JDet-74/VIDEO2SCART/3DPrint/case01.jpg

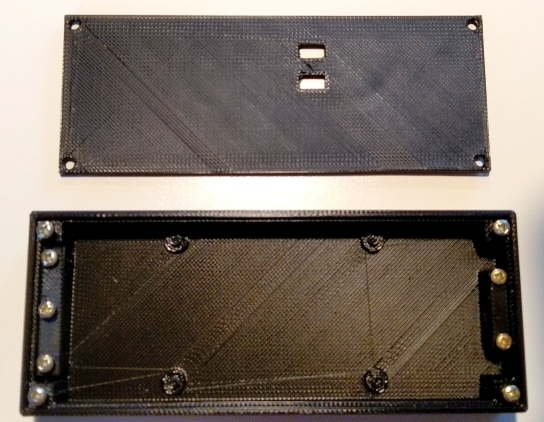
3DPrint/case01.jpg
