JDet-74/VIDEO2SCART/3DPrint/case02.jpg

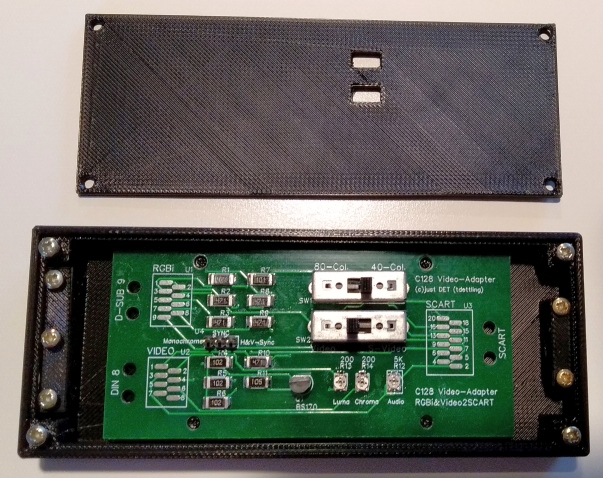
3DPrint/case02.jpg
