JDet-74/VIDEO2SCART/3DPrint/case03.jpg

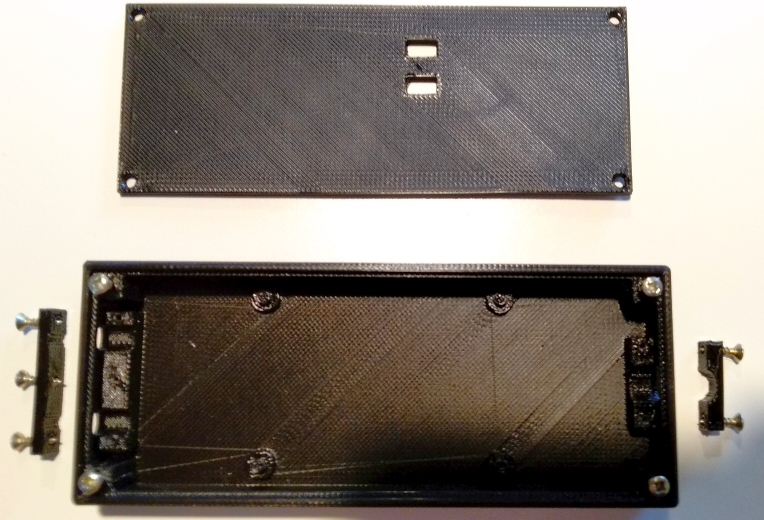
3DPrint/case03.jpg
