JDet-74/VIDEO2SCART/3DPrint/case04.jpg

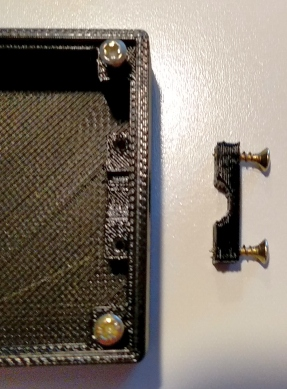
3DPrint/case04.jpg
