JDet-74/VIDEO2SCART/3DPrint/case05.jpg

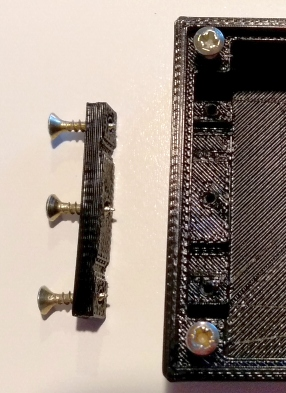
3DPrint/case05.jpg
