JDet-74/VIDEO2SCART/3DPrint/case06.jpg

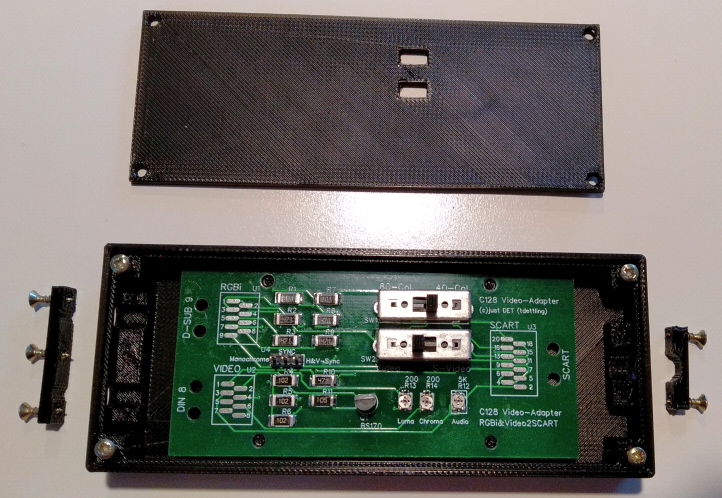
3DPrint/case06.jpg
