JDet-74/VIDEO2SCART/cable_howto/cable_03.jpg

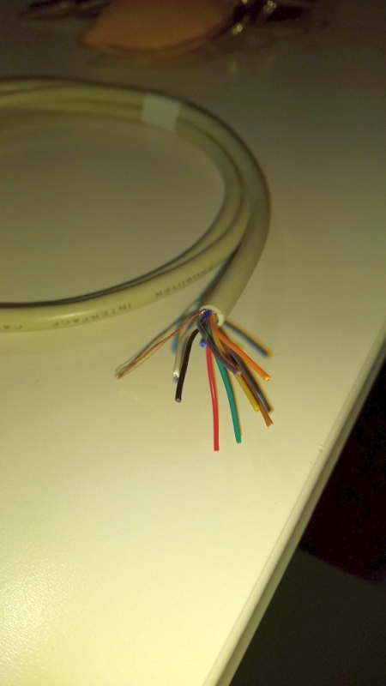
cable_howto/cable_03.jpg
