JDet-74/VIDEO2SCART/cable_howto/cable_04.jpg

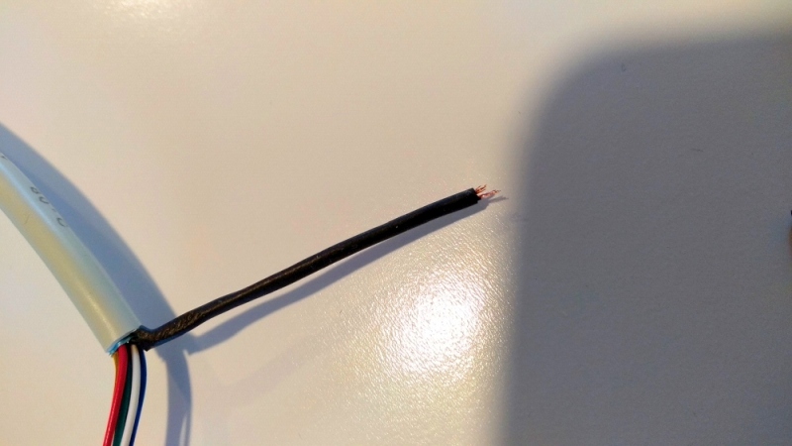
cable_howto/cable_04.jpg
