JDet-74/VIDEO2SCART/cable_howto/cable_04b.jpg

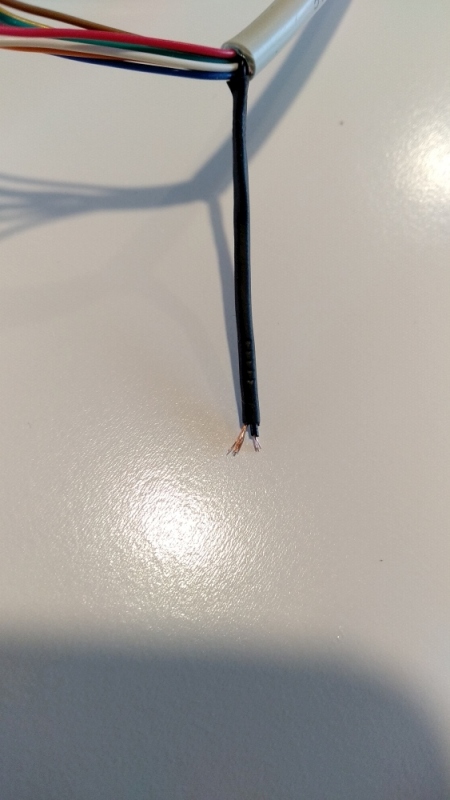
cable_howto/cable_04b.jpg
