JDet-74/VIDEO2SCART/cable_howto/cable_05.jpg

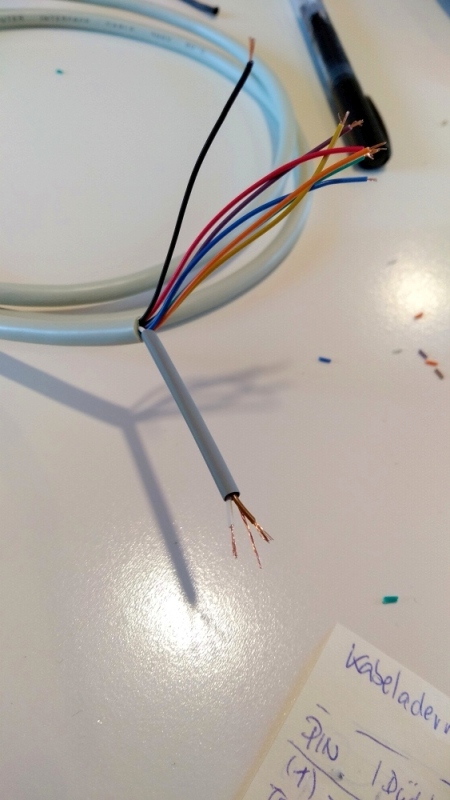
cable_howto/cable_05.jpg
