JDet-74/VIDEO2SCART/cable_howto/cable_05b.jpg

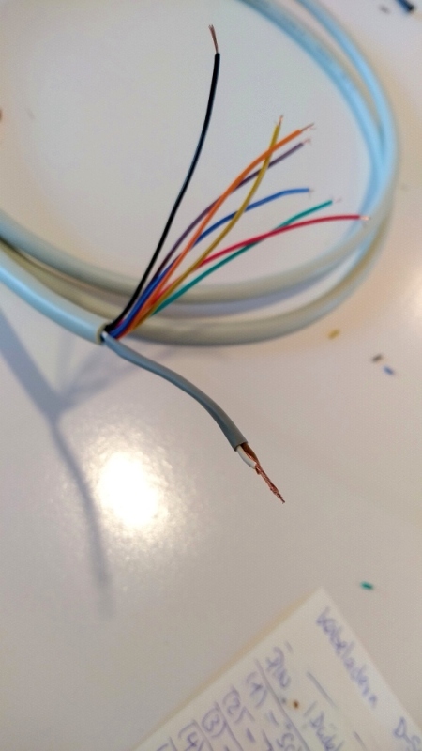
cable_howto/cable_05b.jpg
