JDet-74/VIDEO2SCART/cable_howto/cable_06.jpg

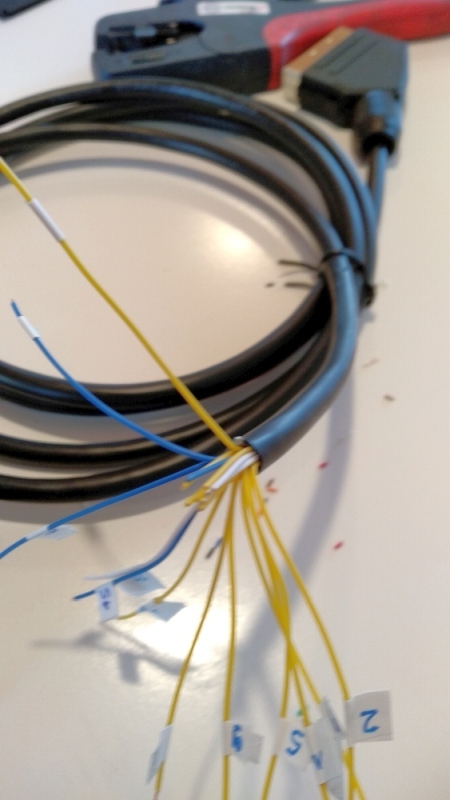
cable_howto/cable_06.jpg
