JDet-74/VIDEO2SCART/cable_howto/cable_07.jpg

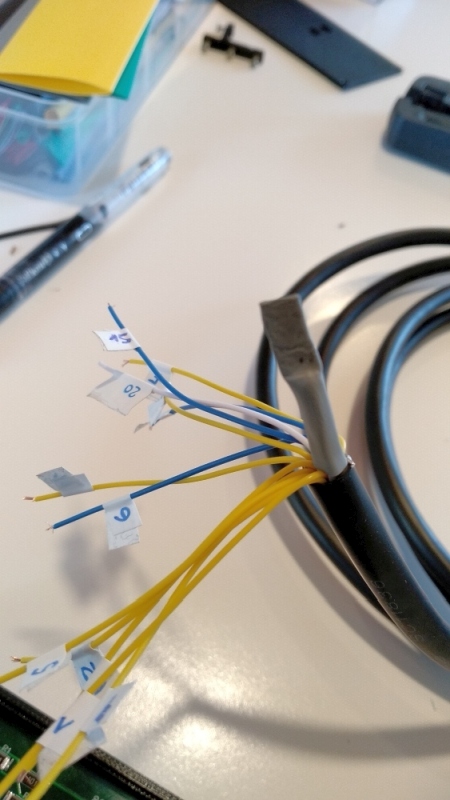
cable_howto/cable_07.jpg
