JDet-74/VIDEO2SCART/cable_howto/cable_08.jpg

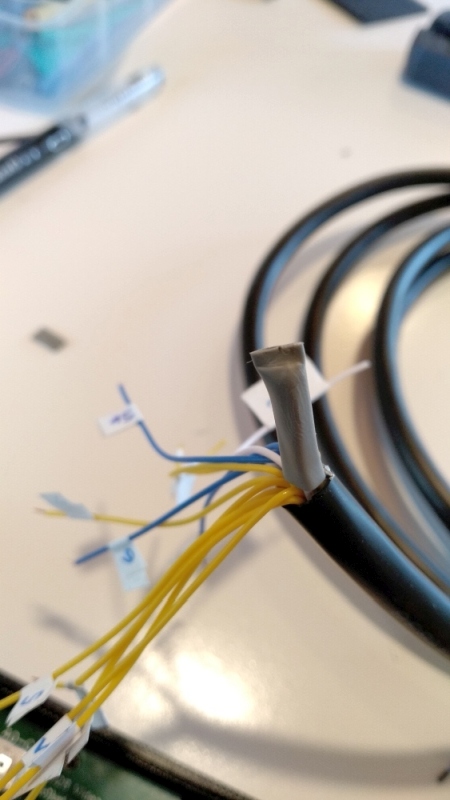
cable_howto/cable_08.jpg
