JDet-74/VIDEO2SCART/cable_howto/cable_09.jpg

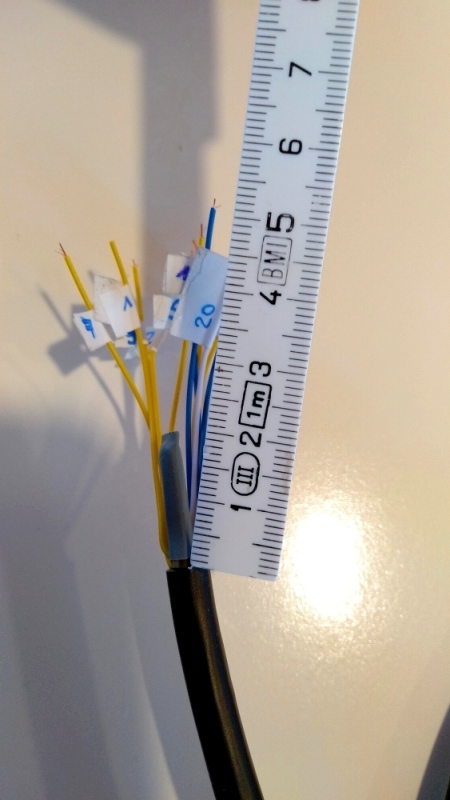
cable_howto/cable_09.jpg
