JDet-74/VIDEO2SCART/cable_howto/cable_10.jpg

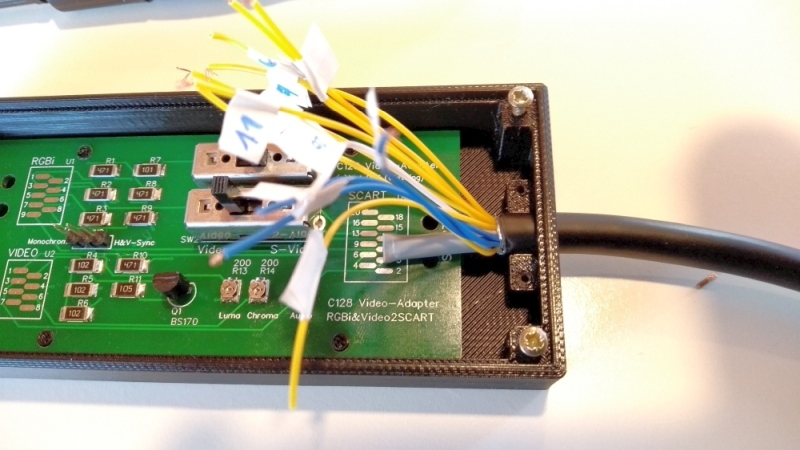
cable_howto/cable_10.jpg
