JDet-74/VIDEO2SCART/cable_howto/cable_11.jpg

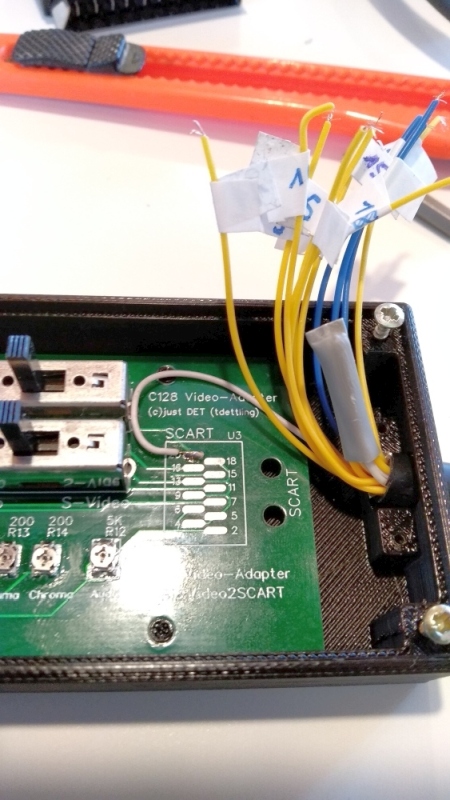
cable_howto/cable_11.jpg
