JDet-74/VIDEO2SCART/cable_howto/cable_13.jpg

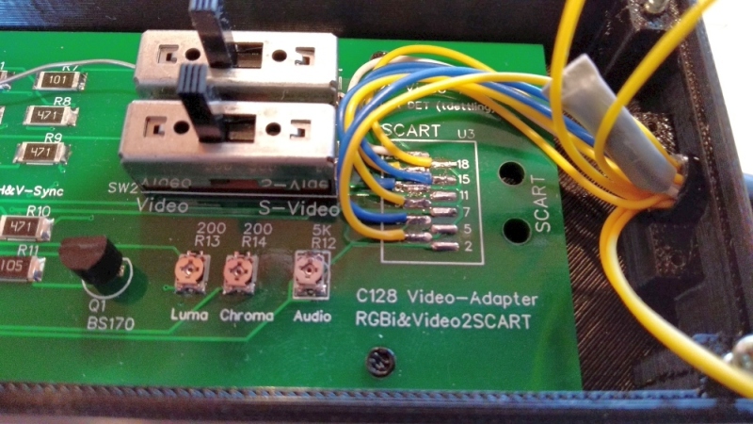
cable_howto/cable_13.jpg
