JDet-74/VIDEO2SCART/cable_howto/cable_15.jpg

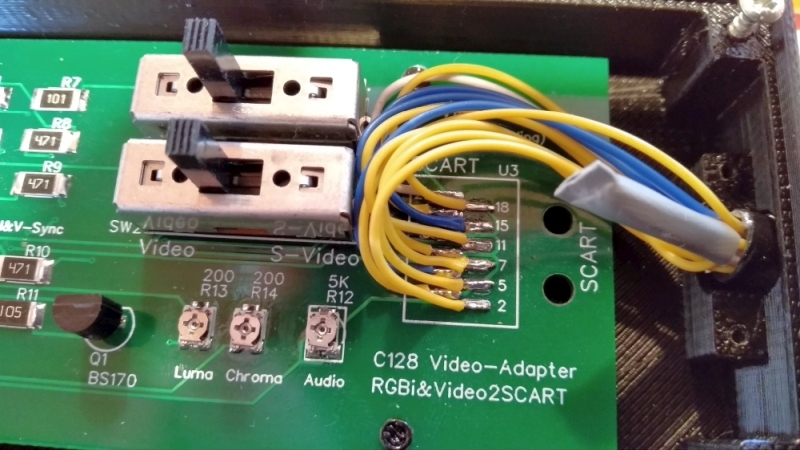
cable_howto/cable_15.jpg
