JDet-74/VIDEO2SCART/cable_howto/cable_16.jpg

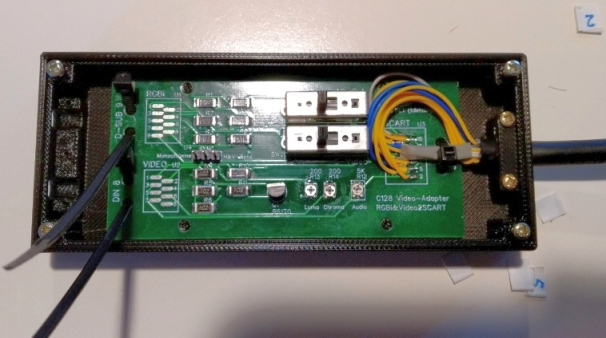
cable_howto/cable_16.jpg
