JDet-74/VIDEO2SCART/cable_howto/cable_17.jpg

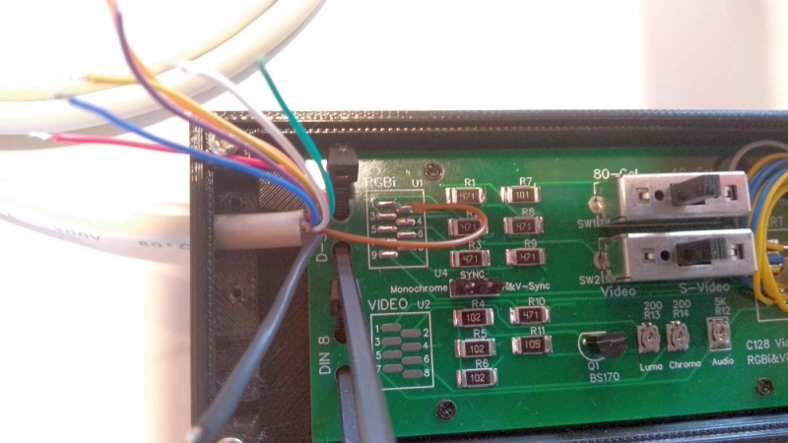
cable_howto/cable_17.jpg
