JDet-74/VIDEO2SCART/cable_howto/cable_19.jpg

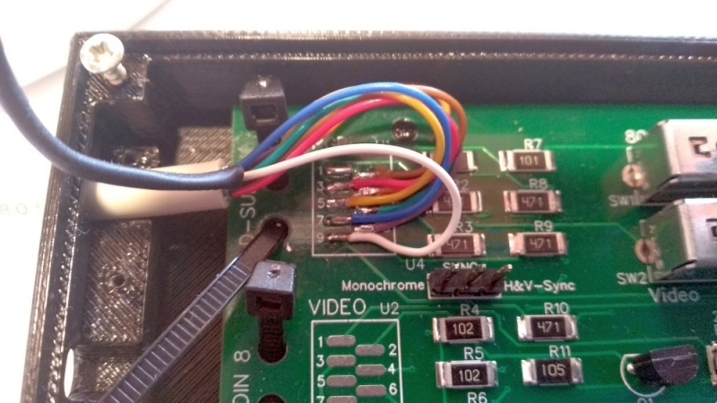
cable_howto/cable_19.jpg
