JDet-74/VIDEO2SCART/cable_howto/cable_20.jpg

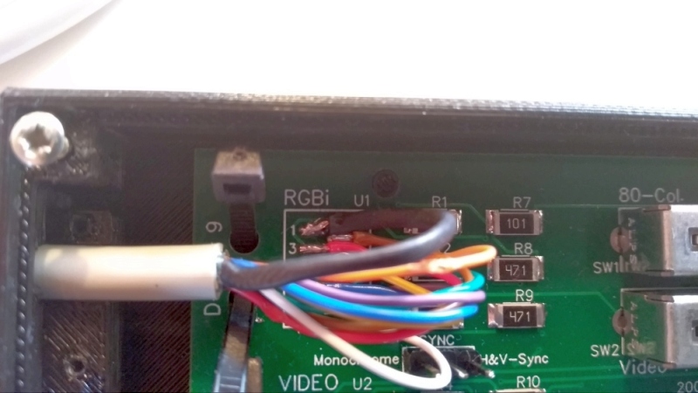
cable_howto/cable_20.jpg
