JDet-74/VIDEO2SCART/cable_howto/cable_21.jpg

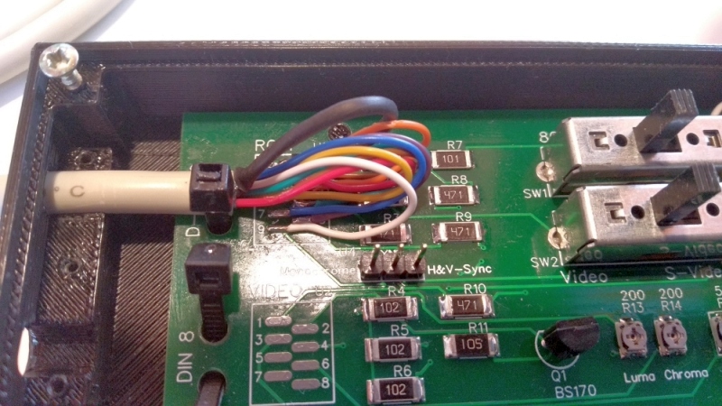
cable_howto/cable_21.jpg
