JDet-74/VIDEO2SCART/cable_howto/cable_22.jpg

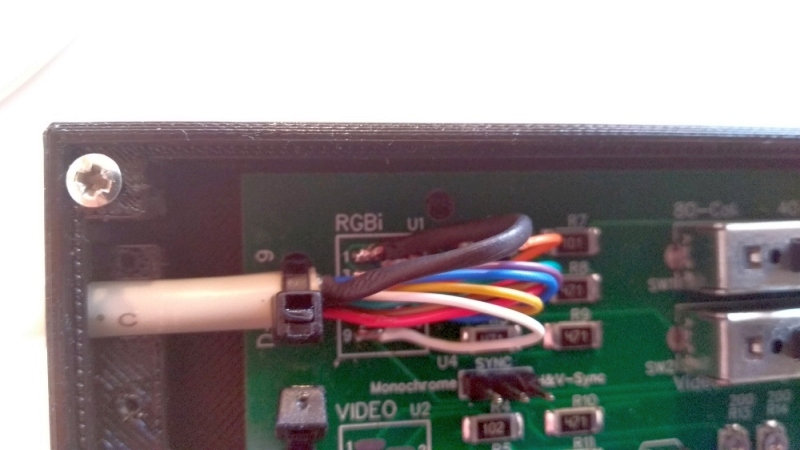
cable_howto/cable_22.jpg
