JDet-74/VIDEO2SCART/cable_howto/cable_23.jpg

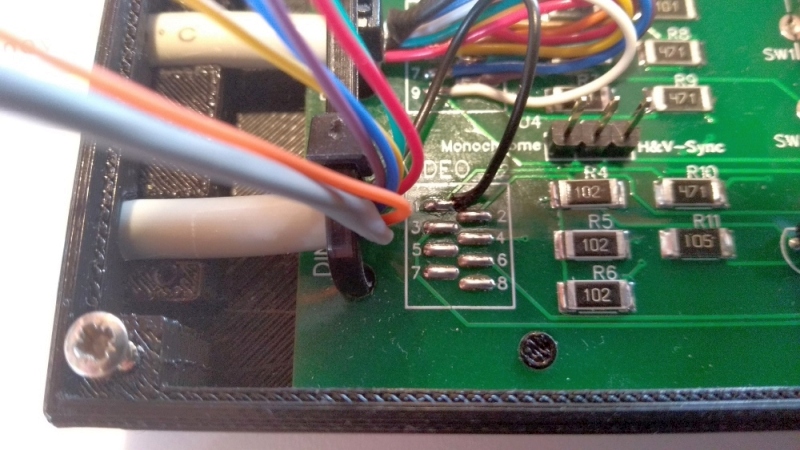
cable_howto/cable_23.jpg
