JDet-74/VIDEO2SCART/cable_howto/cable_24.jpg

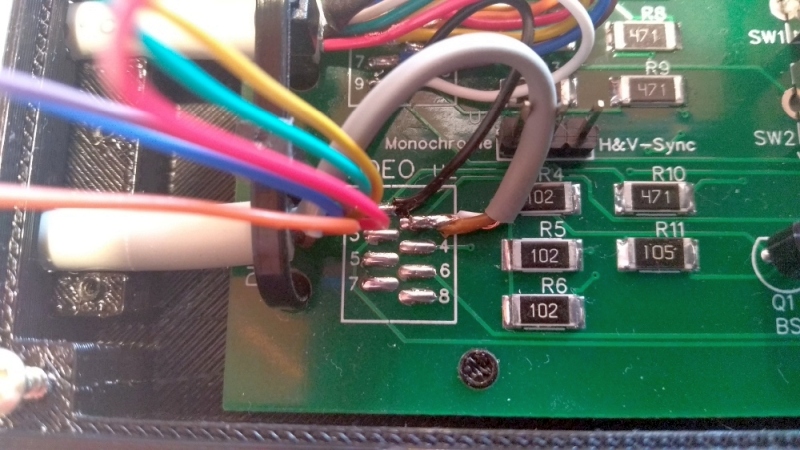
cable_howto/cable_24.jpg
