JDet-74/VIDEO2SCART/cable_howto/cable_25.jpg

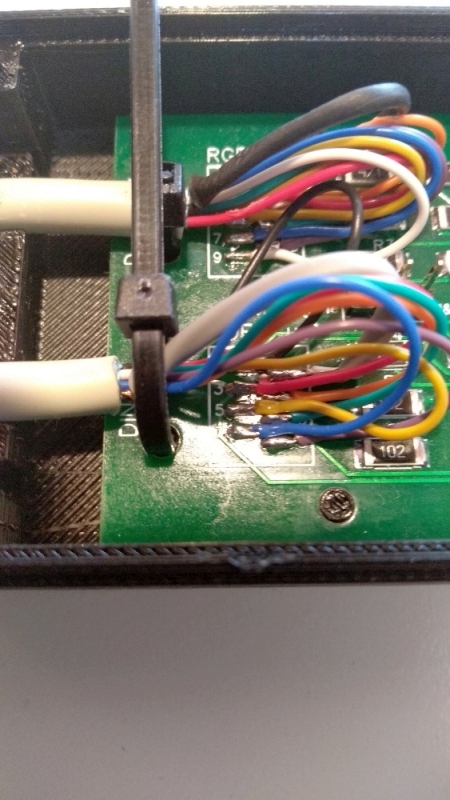
cable_howto/cable_25.jpg
