JDet-74/VIDEO2SCART/cable_howto/cable_26.jpg

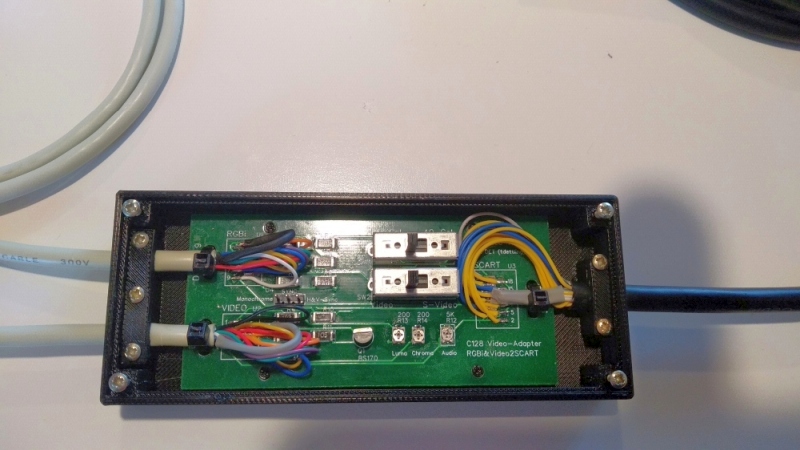
cable_howto/cable_26.jpg
