JDet-74/VIDEO2SCART/cable_howto/cable_27.jpg

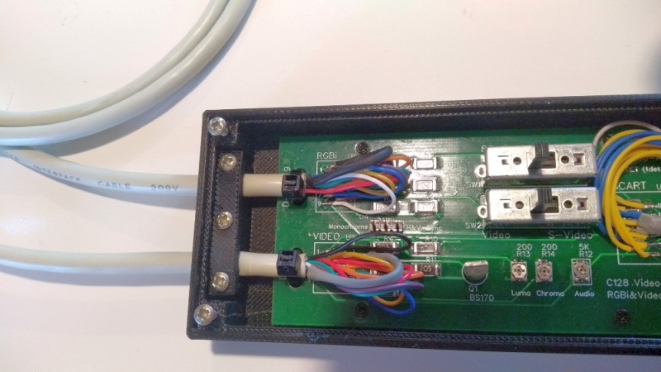
cable_howto/cable_27.jpg
