JDet-74/VIDEO2SCART/cable_howto/cable_28.jpg

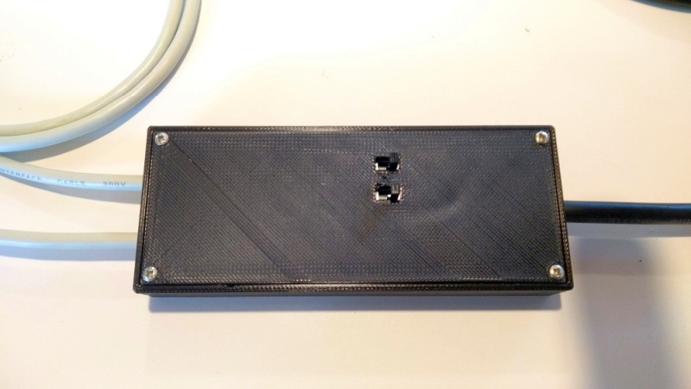
cable_howto/cable_28.jpg
