JDet-74/VIDEO2SCART/cable_howto/cable_31.jpg

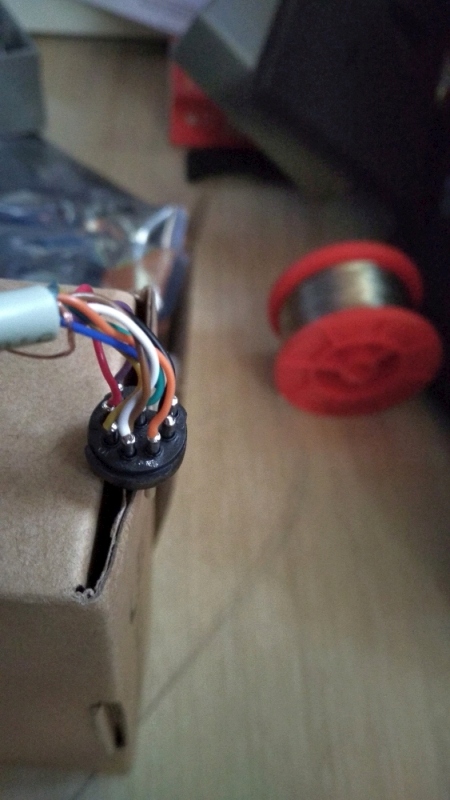
cable_howto/cable_31.jpg
