JDet-74/VIDEO2SCART/cable_howto/cable_32.jpg

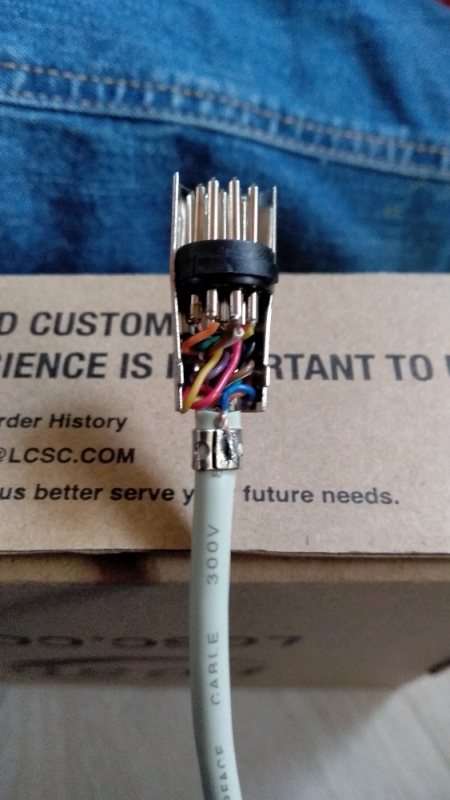
cable_howto/cable_32.jpg
